JAJV02002/PV-Monitoring-System/hardware/pcb/kicad/3dmodels/resistor-CR1206-FX-1003ELF.step

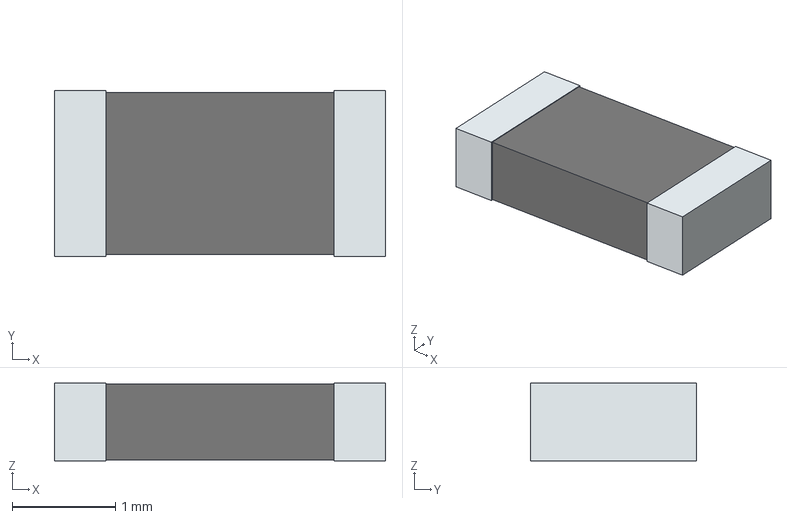
[picture p15: CAD file, 2026-09-22]
hardware/pcb/kicad/3dmodels/resistor-CR1206-FX-1003ELF.step
3.20 x 1.60 x 0.75 mm
term1
term2
