JAJV02002/PV-Monitoring-System/hardware/pcb/kicad/3dmodels/HXS20-NP.step

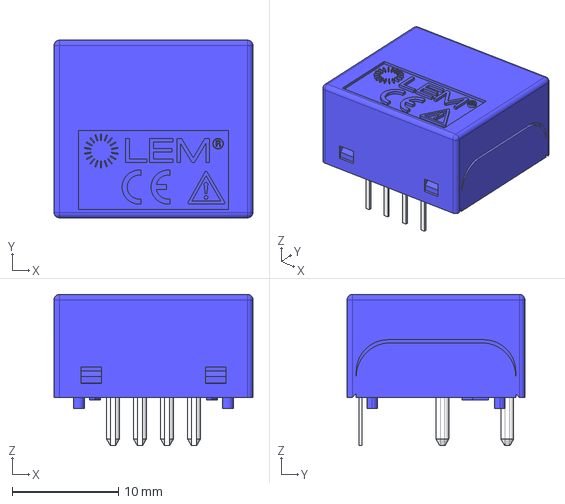
[picture p16: CAD file, 2026-09-22]
hardware/pcb/kicad/3dmodels/HXS20-NP.step
18.7 x 16.7 x 14.2 mm
