JAJV02002/PV-Monitoring-System/hardware/pcb/kicad/3dmodels/HCPL-7800A-300E.step

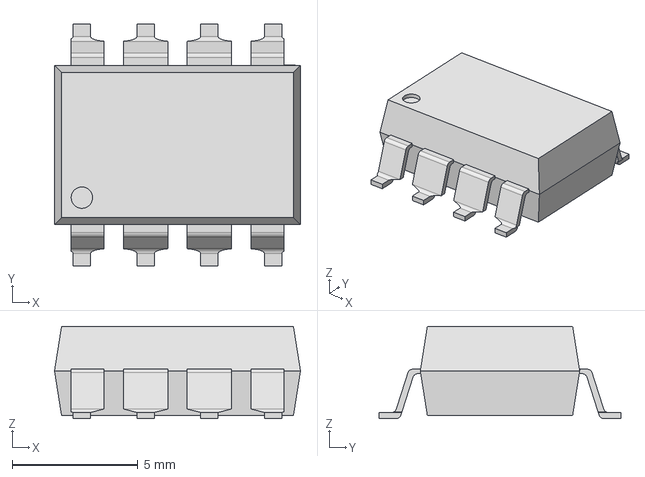
[picture p17: CAD file, 2026-09-22]
hardware/pcb/kicad/3dmodels/HCPL-7800A-300E.step
9.80 x 9.65 x 3.68 mm
