JAJV02002/PV-Monitoring-System/hardware/pcb/kicad/3dmodels/capacitor-TAJS104K020RNJ.step

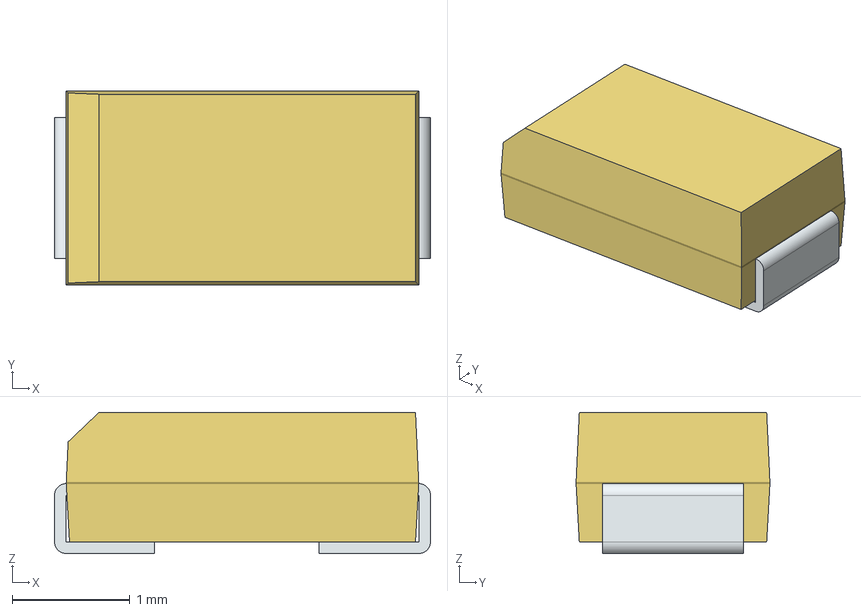
[picture p18: CAD file, 2026-09-22]
hardware/pcb/kicad/3dmodels/capacitor-TAJS104K020RNJ.step
3.20 x 1.65 x 1.20 mm
FilletPin1
FilletPin2
