JAJV02002/PV-Monitoring-System/software/firmware/include/secrets.example.h

#pragma once

#define SERVER_URL "https://example.com/app/api.php"
#define DEVICE_API_KEY "REPLACE_WITH_A_RANDOM_HEXADECIMAL_KEY"
#define WIFI_SSID "YOUR_WIFI_NETWORK"
#define WIFI_PASSWORD "YOUR_WIFI_PASSWORD"
